DedeHai/SolarGardenJarLight/images/IMG_20170708_101516.jpg

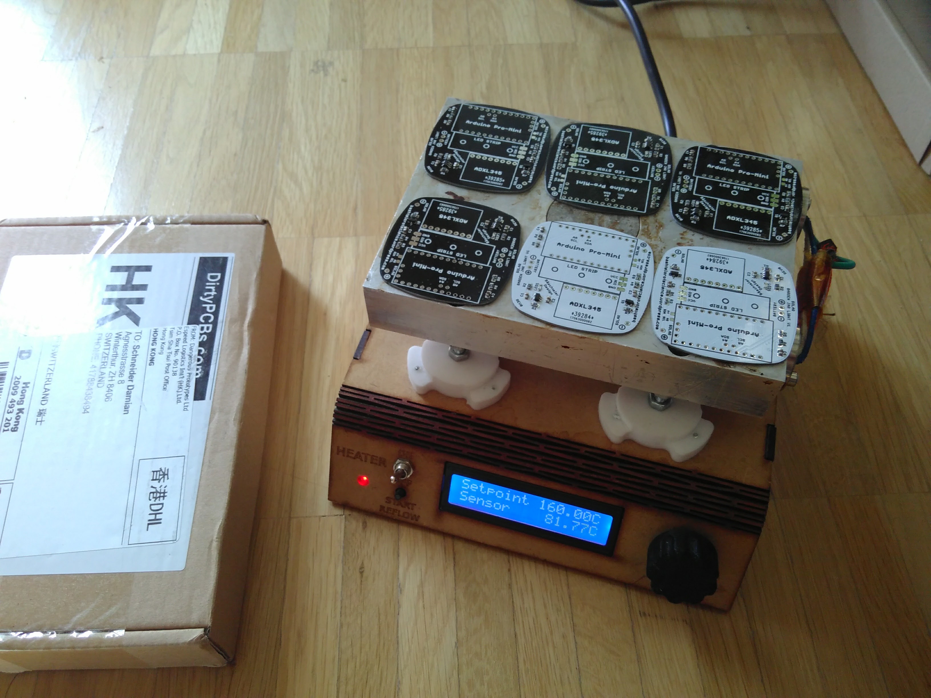
images/IMG_20170708_101516.jpg
