DedeHai/SolarGardenJarLight/images/IMG_20170708_101529.jpg

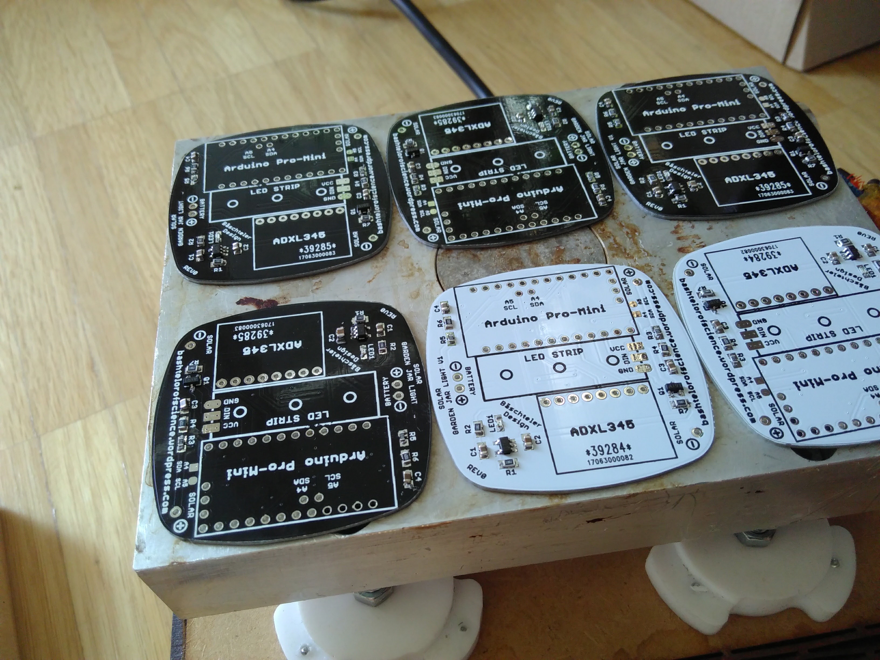
images/IMG_20170708_101529.jpg
