DedeHai/SolarGardenJarLight/images/IMG_20170709_111643.jpg

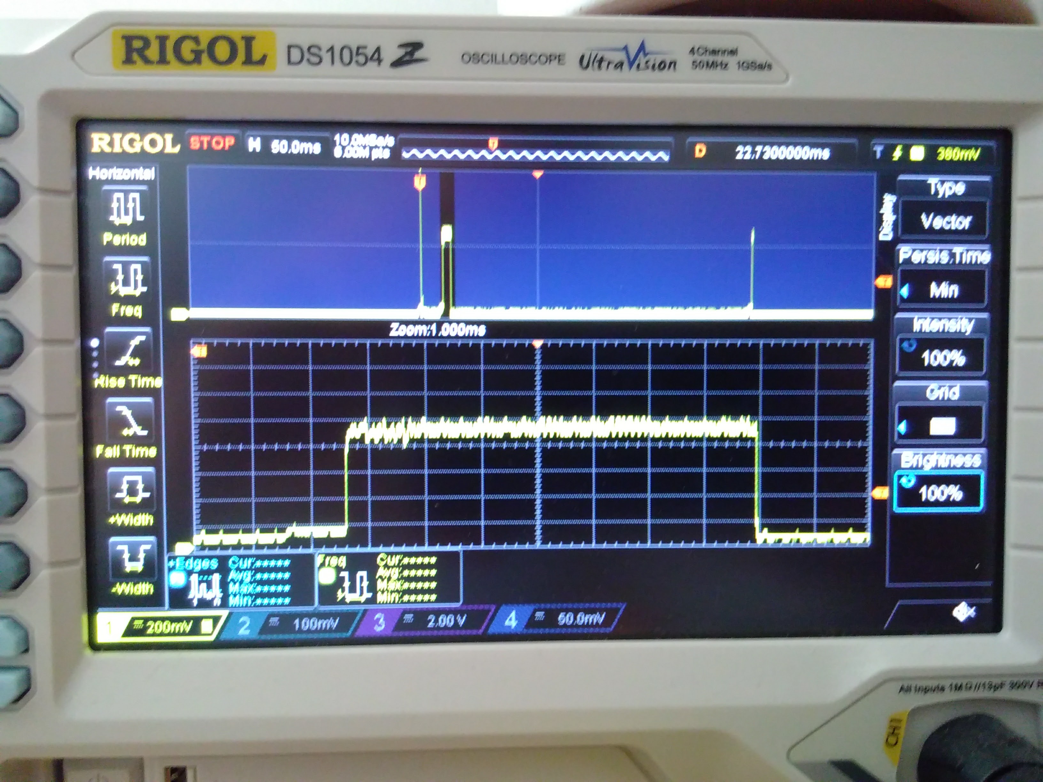
images/IMG_20170709_111643.jpg
