DedeHai/SolarGardenJarLight/images/IMG_20170709_111647.jpg

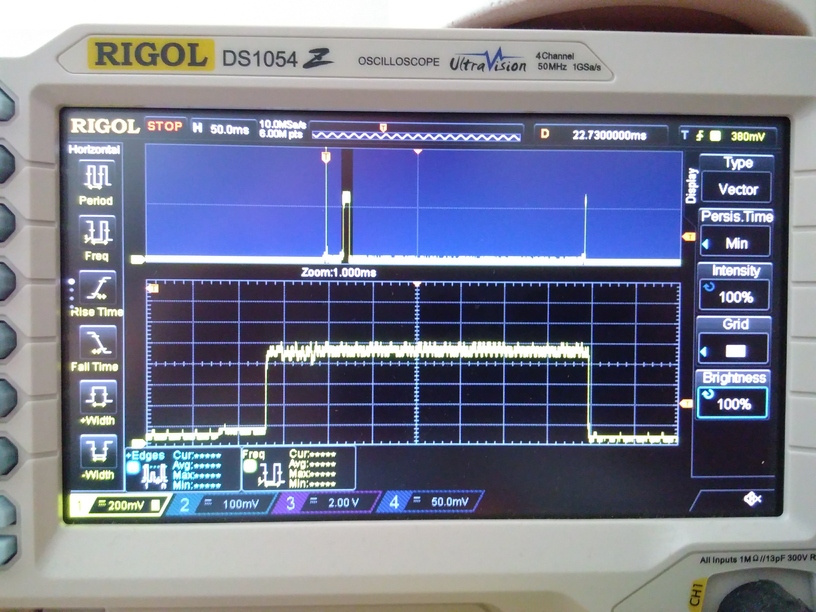
images/IMG_20170709_111647.jpg
