DedeHai/SolarGardenJarLight/images/IMG_20170709_111734.jpg

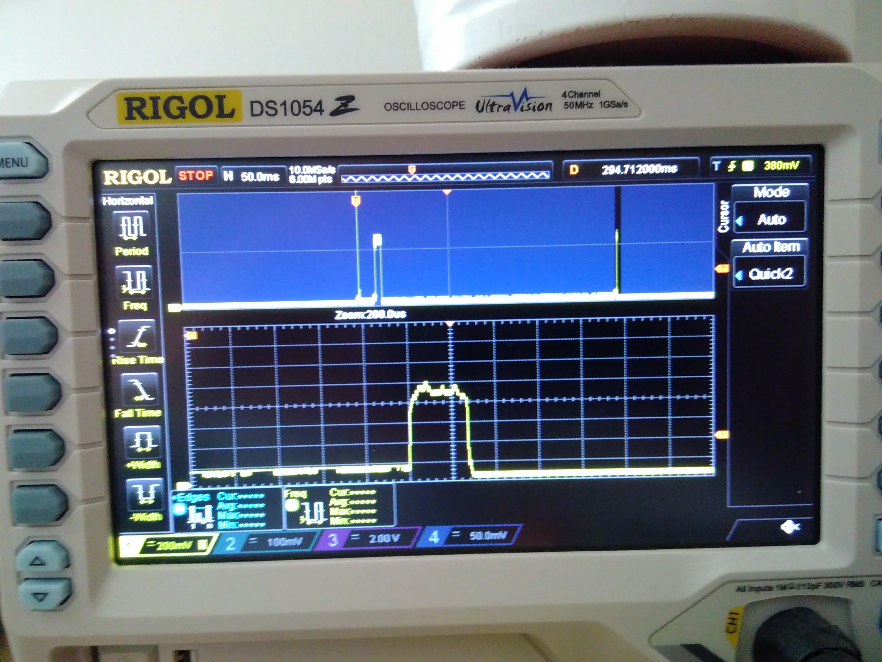
images/IMG_20170709_111734.jpg
