DedeHai/SolarGardenJarLight/images/IMG_20170709_111807.jpg

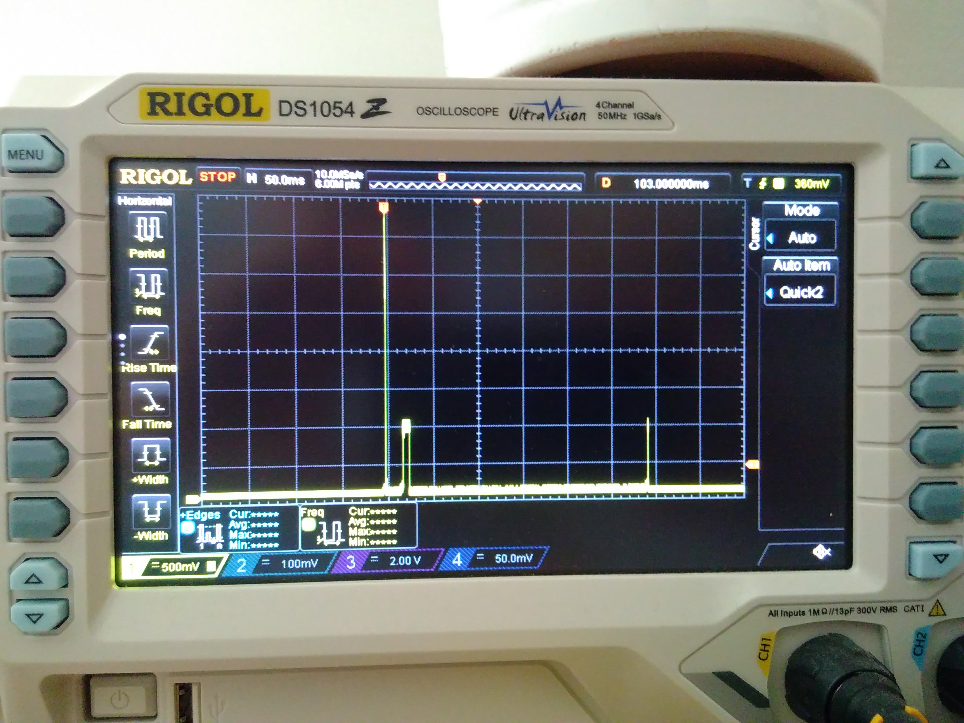
images/IMG_20170709_111807.jpg
