DedeHai/SolarGardenJarLight/images/IMG_20170709_111839.jpg

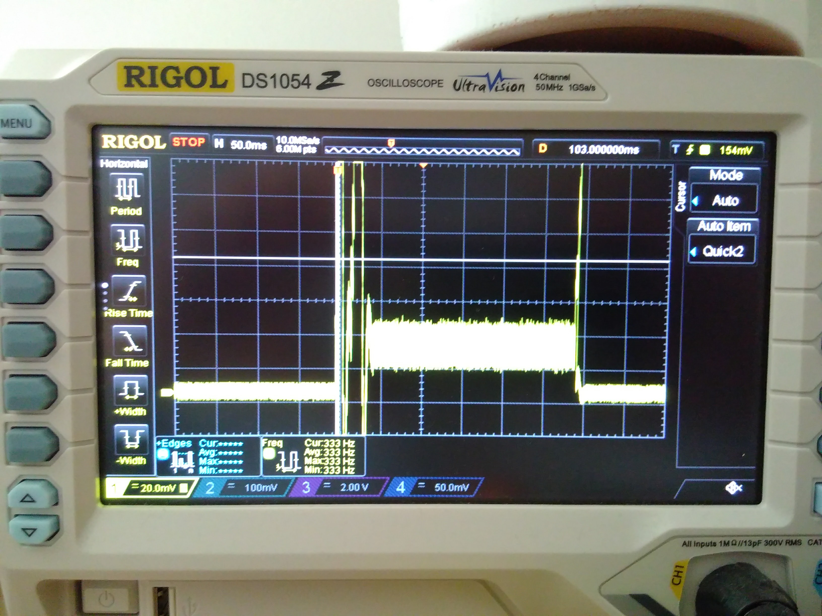
images/IMG_20170709_111839.jpg
