DedeHai/SolarGardenJarLight/images/IMG_20170709_112256.jpg

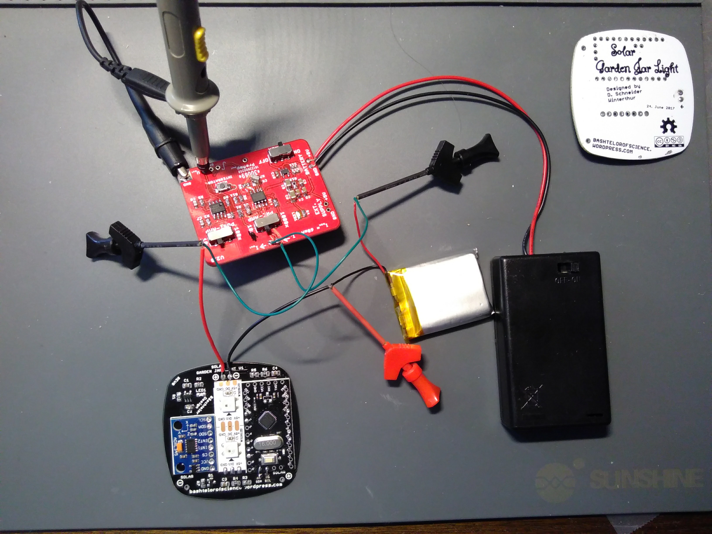
images/IMG_20170709_112256.jpg
