DedeHai/SolarGardenJarLight/images/IMG_20170709_112258.jpg

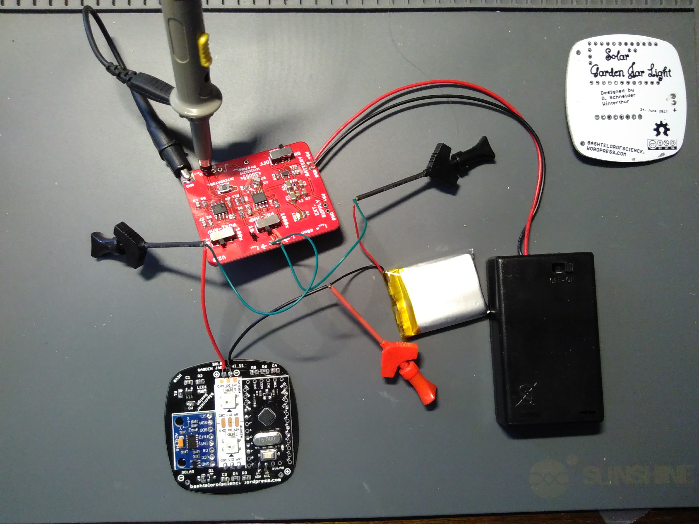
images/IMG_20170709_112258.jpg
