DedeHai/SolarGardenJarLight/images/lowres-zusammenstellung.JPG

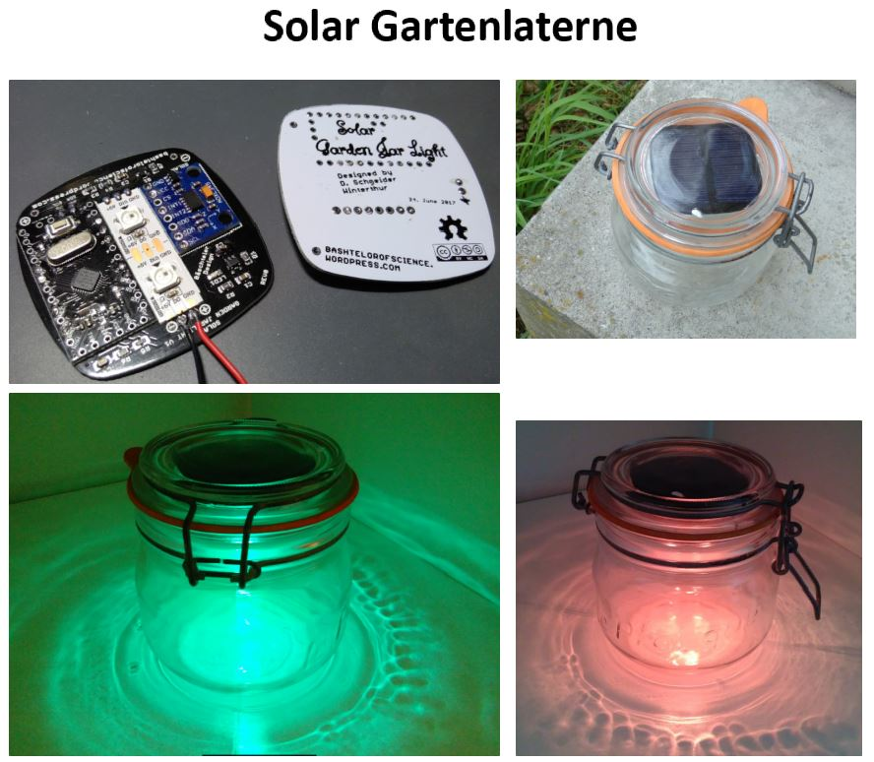
images/lowres-zusammenstellung.JPG
