DedeHai/SolarGardenJarLight/Firmware/GardenJarLight/led_stuff.ino

/*************************
  SOLAR GARDEN JAR LIGHT

  by Damian Schneider
 *************************

   Copyright (c) Damian Schneider 2017

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
   You should have received a copy of the GNU General Public License along with
   this program. If not, see <http://www.gnu.org/licenses/>.
*/


void updateLEDs(CHSV sendcolor)
{
  fill_solid(leds, NUM_LEDS, sendcolor);
  FastLED.show(); // display this frame
}


//fade out and switch leds of
void switchLEDoff(bool usefadeout)
{
  uint8_t startbrightness = ledcolor_hsv.v;
  uint8_t i;
  if (usefadeout)
  {
    for (i = ledcolor_hsv.v; i > 0; i--)
    {
      ledcolor_hsv.v = i;
      updateLEDs(ledcolor_hsv);
      delay(9);
      wdt_reset(); //kick the watchdog
    }
  }
  ledcolor_hsv.v = startbrightness; //set the global variable back to the previous brightness
  running = false;
  autoOn = true; //was running, let the daylight reset this variable to false (i.e. do not switch back on if it is dark outside)

  pinMode(LED_PIN, INPUT);
  digitalWrite(LED_PIN, LOW); //LED data pin to high impedance
  pinMode(LEDPWR_PIN, INPUT);
  digitalWrite(LEDPWR_PIN, HIGH); //LEDs OFF

  adxl_powerdown(); //set accelerometer power power and I2C pins low
}

//fade in and go to running mode
void switchLEDon(bool usefadein)
{
  pinMode(LEDPWR_PIN, OUTPUT);
  digitalWrite(LEDPWR_PIN, LOW); //LEDs ON
  delay(2); //wait for led voltage to be stable
  pinMode(LED_PIN, OUTPUT); //set data pin as output again
   
  running = true;
  minutecounter = 0; //reset minute counter
  //led fade in to currently set brightness
  uint8_t endbrightness = ledcolor_hsv.v;
  uint8_t i;
  if (usefadein)
  {
    for (i = 0; i < endbrightness; i++)
    {
      ledcolor_hsv.v = i;
      updateLEDs(ledcolor_hsv);
      delay(7);
      wdt_reset(); //kick the watchdog
    }
  }

}


void lowVoltageWarning(void) {
  uint8_t i;
  CHSV warnincolor;
  switchLEDon(false);

  warnincolor.h = 0; //blink in red

  warnincolor.s = 255;

  for (i = 0; i < 5; i++) {
    warnincolor.v = 220;
    updateLEDs(warnincolor);
    //  LowPower.powerDown(SLEEP_60MS, ADC_OFF, BOD_OFF);
    powerDown(WDTO_60MS);
    warnincolor.v = 0;
    updateLEDs(warnincolor);
    //   LowPower.powerDown(SLEEP_250MS, ADC_OFF, BOD_OFF);
    powerDown(WDTO_250MS);
    wdt_reset(); //kick the watchdog
  }
  switchLEDoff(false);
}
